victor-chew/rbx/freecad/servo/Printed_SG90_Servo_Connector/files/9g_conn_top.stl

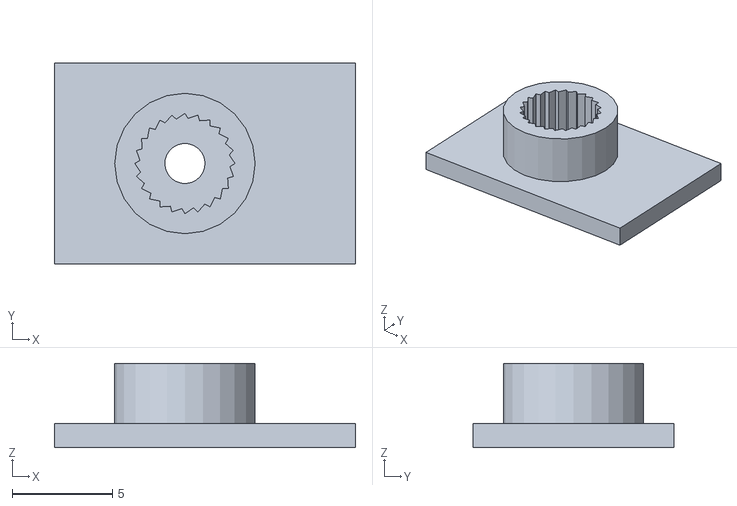
[picture p17: CAD file, 2021-03-17]
freecad/servo/Printed_SG90_Servo_Connector/files/9g_conn_top.stl
15.0 x 10.0 x 4.20
