victor-chew/rbx/freecad/sonar/back.stl

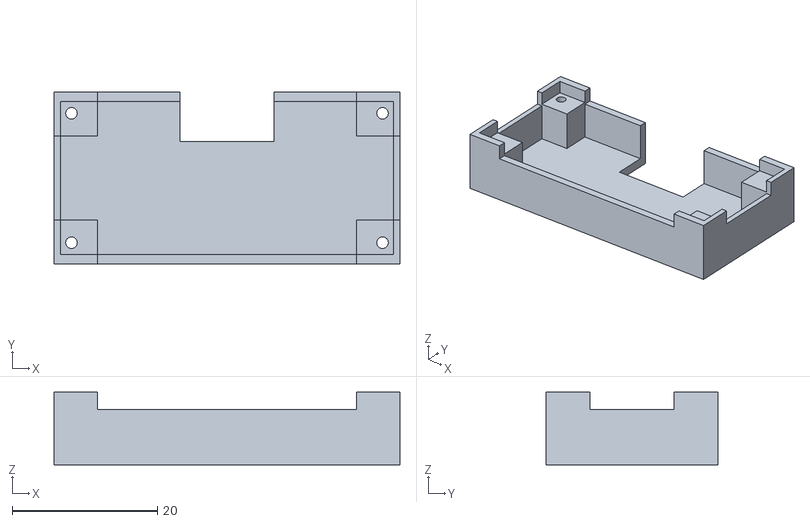
[picture p18: CAD file, 2021-03-17]
freecad/sonar/back.stl
47.6 x 23.6 x 10.0
