victor-chew/rbx/freecad/battery-18650/switch-cover.stl

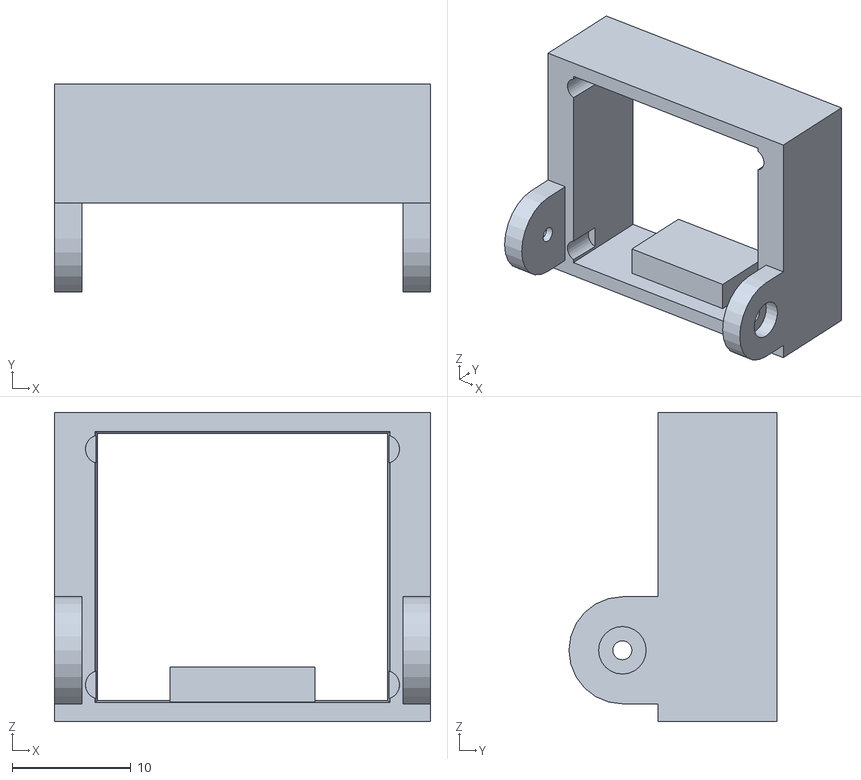
[picture p19: CAD file, 2021-03-17]
freecad/battery-18650/switch-cover.stl
31.6 x 17.5 x 26.0
