victor-chew/rbx/freecad/battery-AA/battery-AA.FCStd

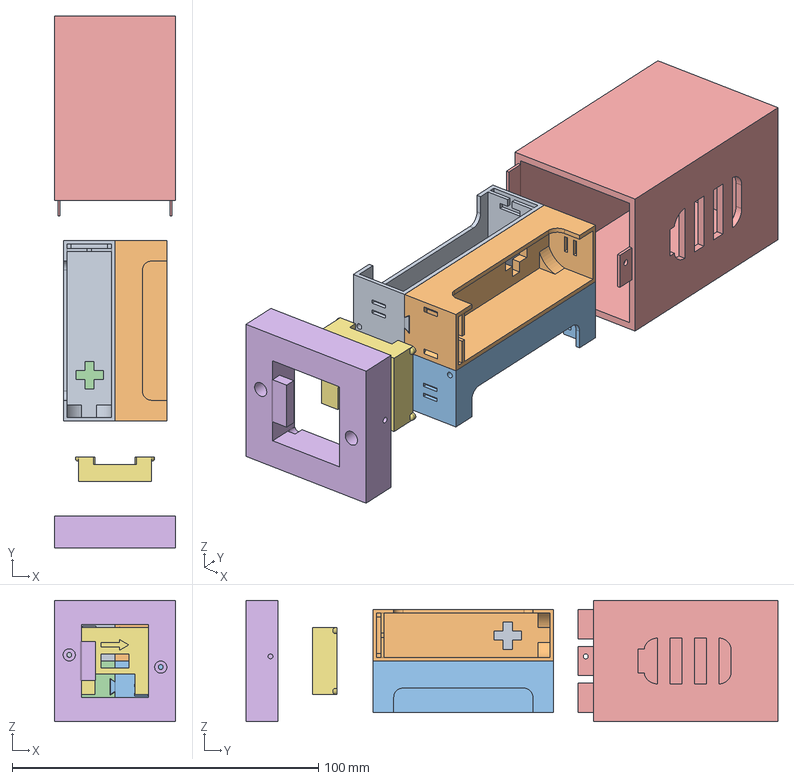
[picture p20: CAD file, 2021-03-17]
freecad/battery-AA/battery-AA.FCStd
39.6 x 173.8 x 39.6 mm
holder
holder-mirror
holder-clone
holder-clone-mirror
bottom
top
switch
