victor-chew/rbx/freecad/brickbase/3x1.3mf

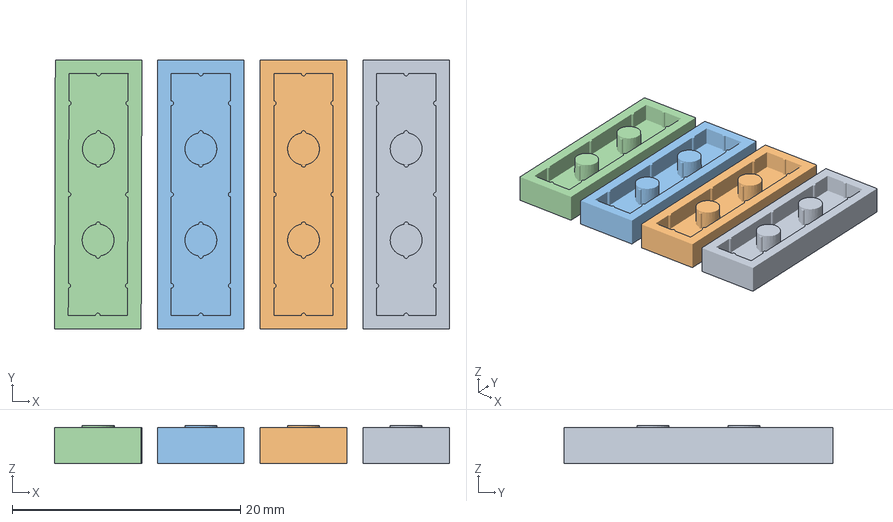
[picture p21: CAD file, 2021-03-17]
freecad/brickbase/3x1.3mf
34.6 x 23.6 x 3.36 mm
3x1.stl
3x1.stl(2)
3x1.stl(3)
3x1.stl(4)
