victor-chew/rbx/freecad/color-sensor/bottom.stl

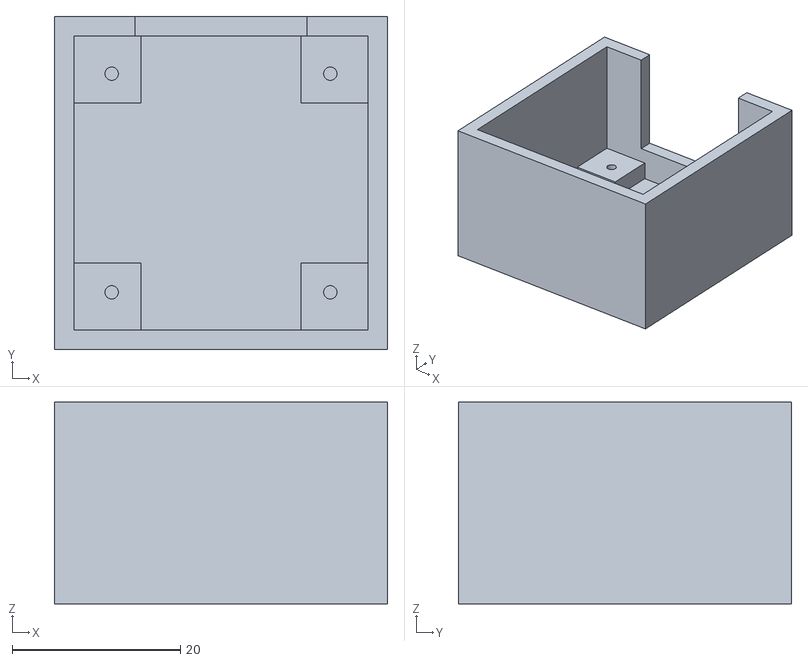
[picture p22: CAD file, 2021-03-17]
freecad/color-sensor/bottom.stl
39.6 x 39.6 x 24.0
