victor-chew/rbx/freecad/led/bottom.stl

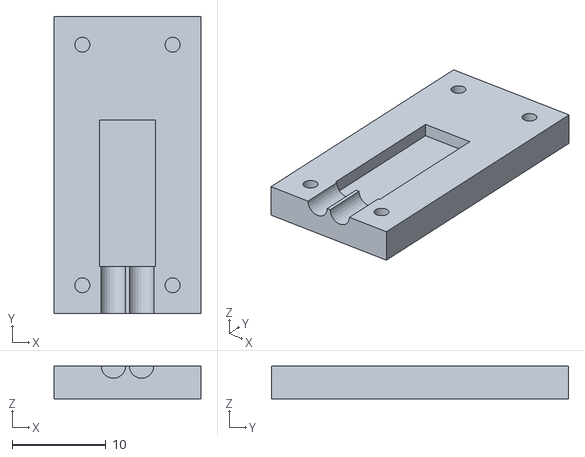
[picture p23: CAD file, 2021-03-17]
freecad/led/bottom.stl
15.6 x 31.6 x 3.50
