victor-chew/rbx/freecad/microcontroller/top.stl

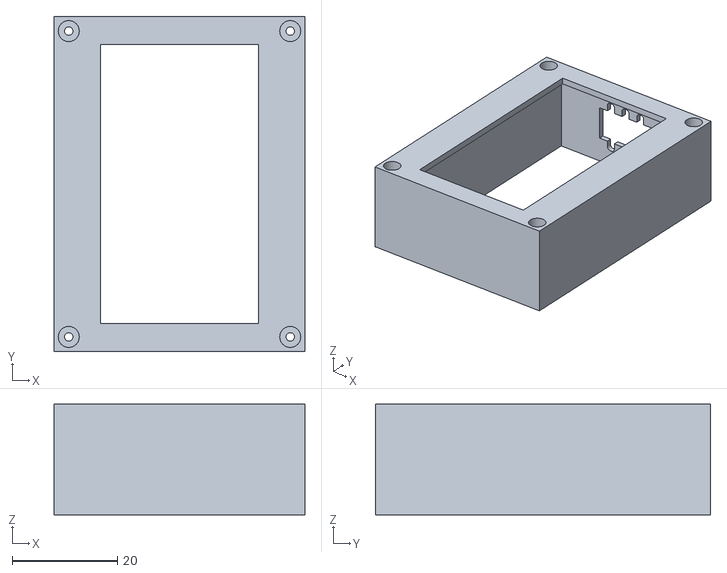
[picture p24: CAD file, 2021-03-17]
freecad/microcontroller/top.stl
47.6 x 63.6 x 21.0
