victor-chew/rbx/freecad/motor-power/motor-power.FCStd

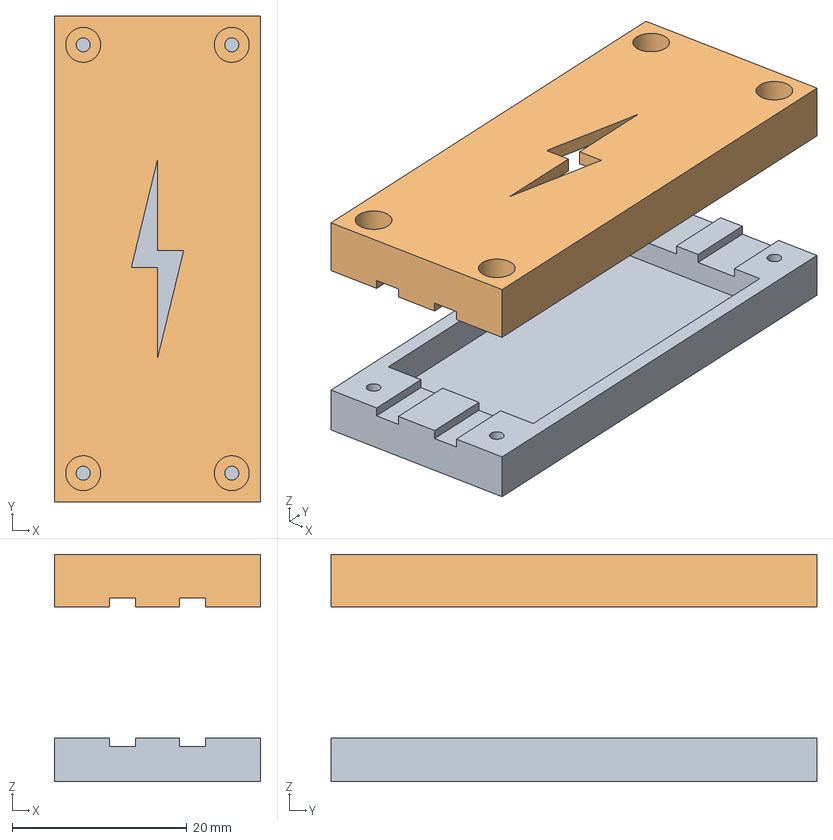
[picture p25: CAD file, 2021-03-17]
freecad/motor-power/motor-power.FCStd
23.6 x 55.6 x 26.0 mm
bottom
top
