victor-chew/rbx/freecad/motor/axle-adapter.stl

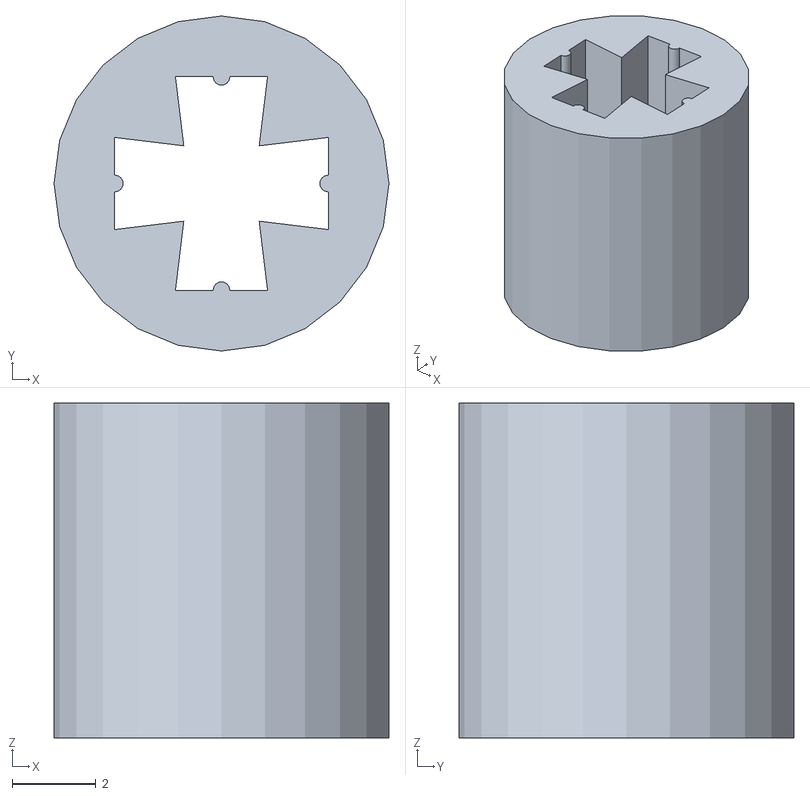
[picture p26: CAD file, 2021-03-17]
freecad/motor/axle-adapter.stl
8.00 x 8.00 x 8.00
