victor-chew/rbx/freecad/oled-display/top.stl

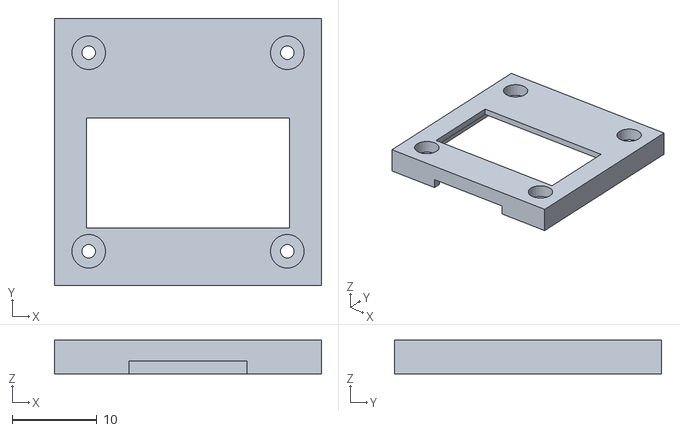
[picture p27: CAD file, 2021-03-17]
freecad/oled-display/top.stl
31.6 x 31.6 x 4.00
