victor-chew/rbx/freecad/photoresistor/top.stl

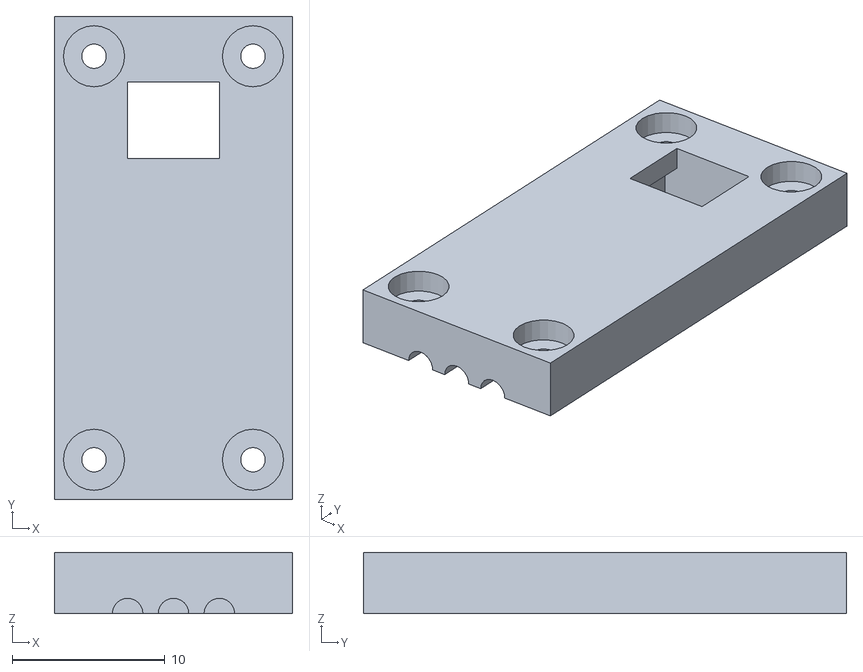
[picture p28: CAD file, 2021-03-17]
freecad/photoresistor/top.stl
15.6 x 31.6 x 4.00
