victor-chew/rbx/freecad/piezo-buzzer/bottom.stl

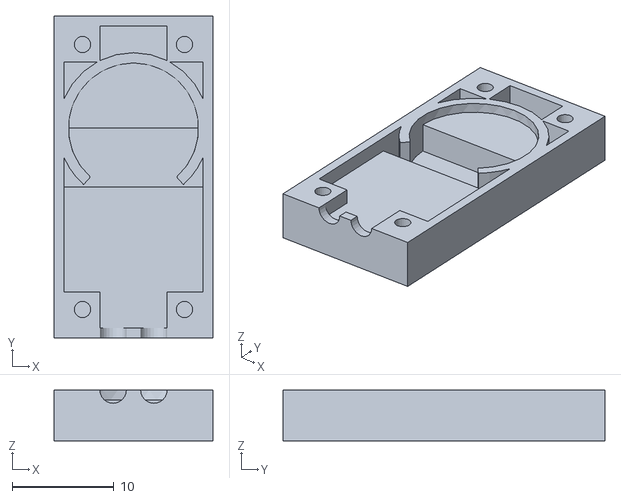
[picture p29: CAD file, 2021-03-17]
freecad/piezo-buzzer/bottom.stl
15.6 x 31.6 x 5.00
