victor-chew/rbx/freecad/pushbutton/top.stl

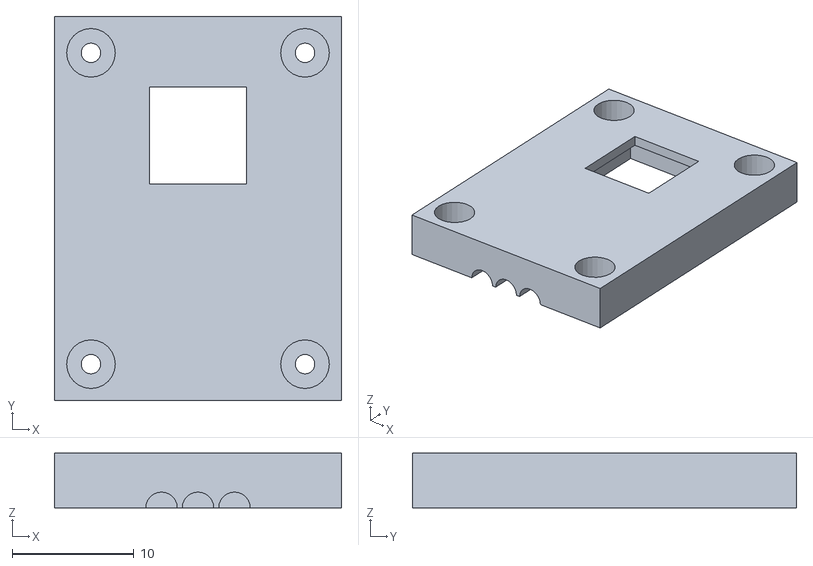
[picture p30: CAD file, 2021-03-17]
freecad/pushbutton/top.stl
23.6 x 31.6 x 4.50
