victor-chew/rbx/freecad/rotary-switch/bottom.stl

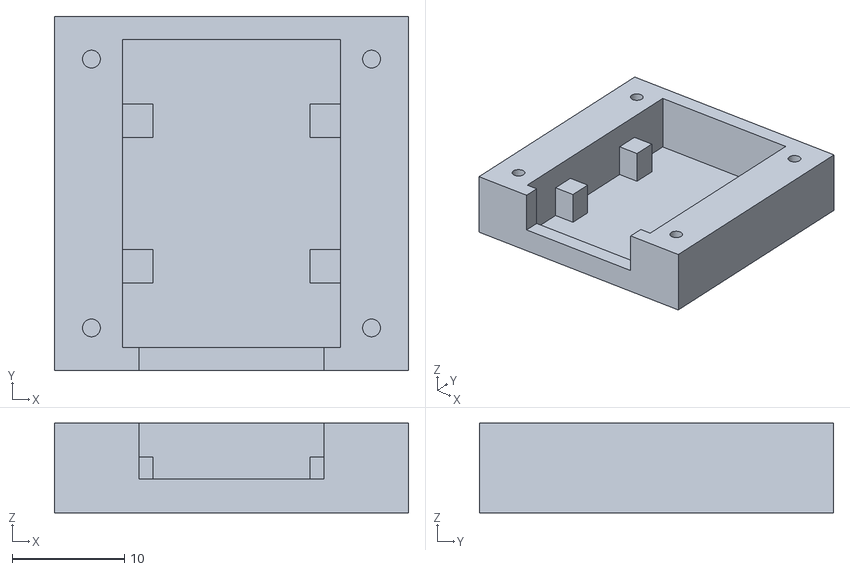
[picture p31: CAD file, 2021-03-17]
freecad/rotary-switch/bottom.stl
31.6 x 31.6 x 8.00
