victor-chew/rbx/freecad/servo/L-bracket.stl

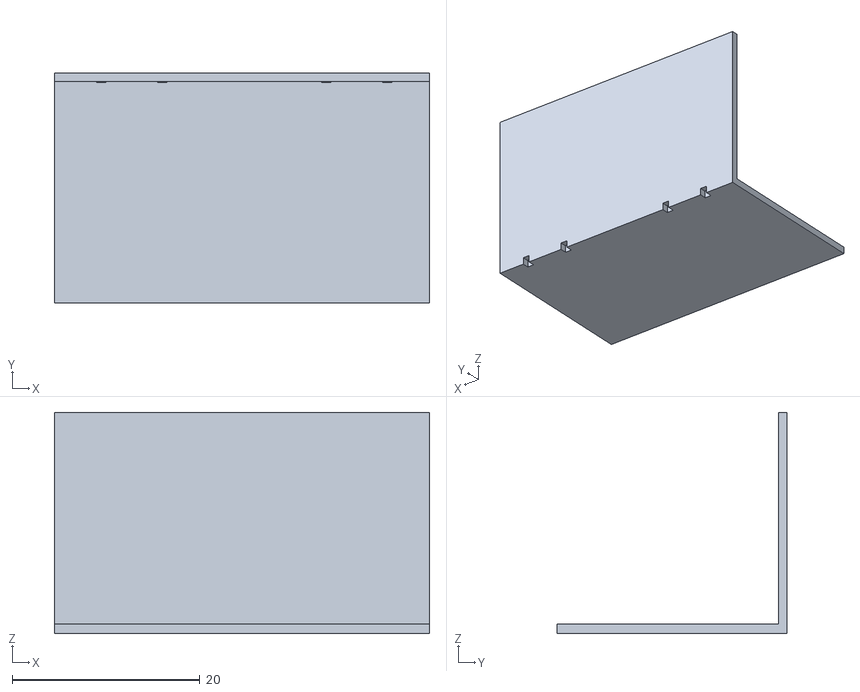
[picture p32: CAD file, 2021-03-17]
freecad/servo/L-bracket.stl
40.0 x 24.5 x 23.6
