victor-chew/rbx/freecad/sonar/front.stl

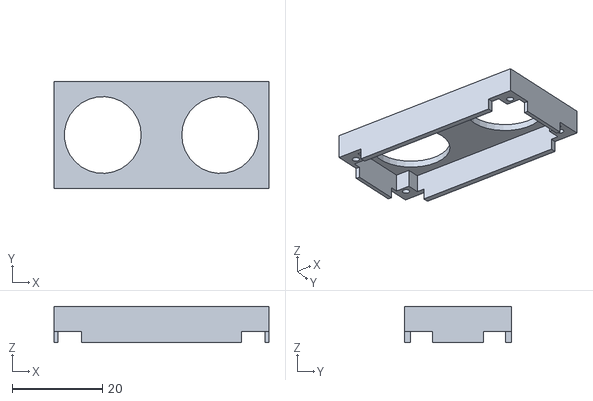
[picture p33: CAD file, 2021-03-17]
freecad/sonar/front.stl
47.6 x 23.6 x 8.00
