victor-chew/rbx/freecad/battery-18650/top.stl

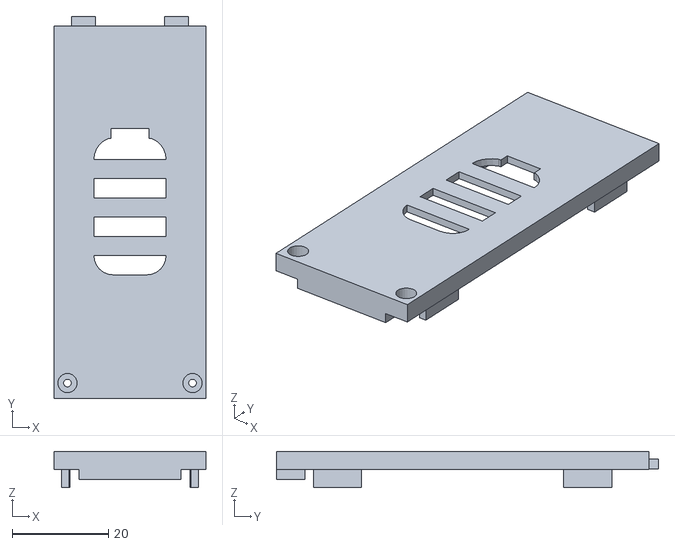
[picture p34: CAD file, 2021-03-17]
freecad/battery-18650/top.stl
31.6 x 79.5 x 7.50
