victor-chew/rbx/freecad/battery-AA/holder.stl

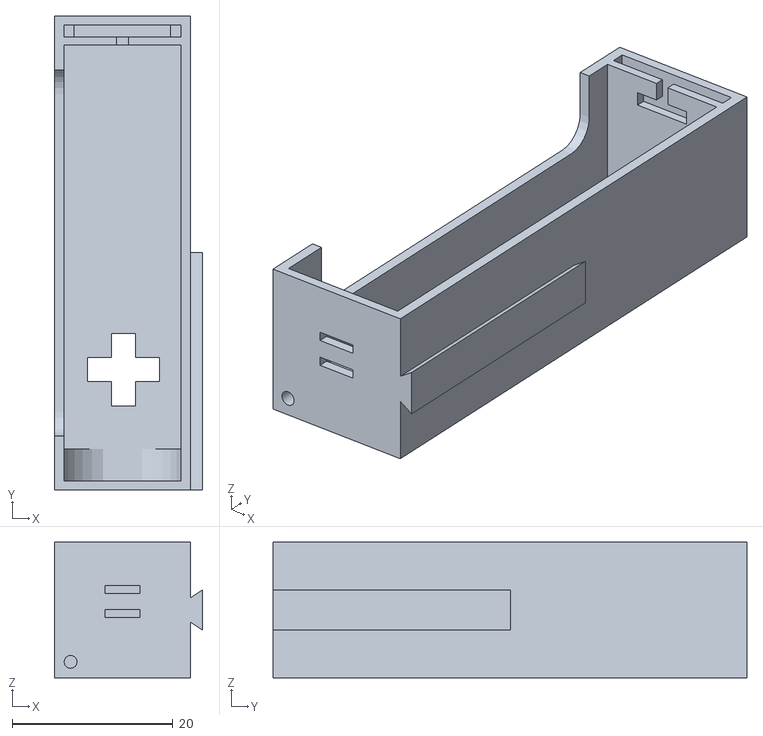
[picture p35: CAD file, 2021-03-17]
freecad/battery-AA/holder.stl
18.4 x 58.9 x 16.9
