victor-chew/rbx/freecad/brickbase/2x1.3mf

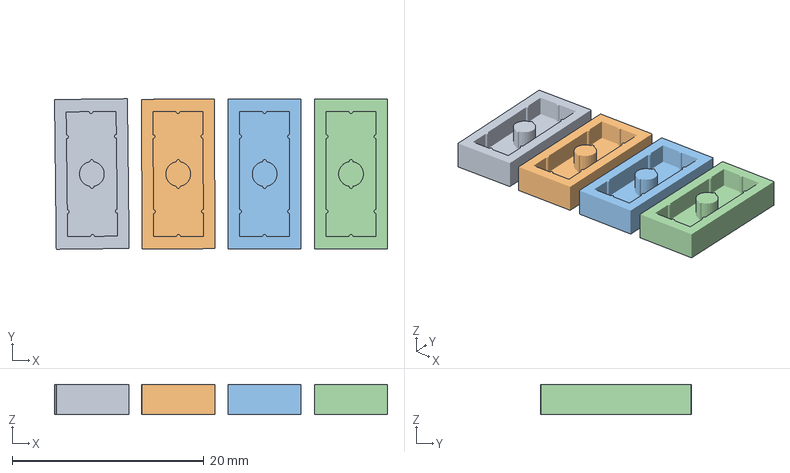
[picture p36: CAD file, 2021-03-17]
freecad/brickbase/2x1.3mf
34.7 x 15.7 x 3.16 mm
2x1.stl
2x1.stl(2)
2x1.stl(4)
2x1.stl(5)
