victor-chew/rbx/freecad/color-sensor/color-sensor.FCStd

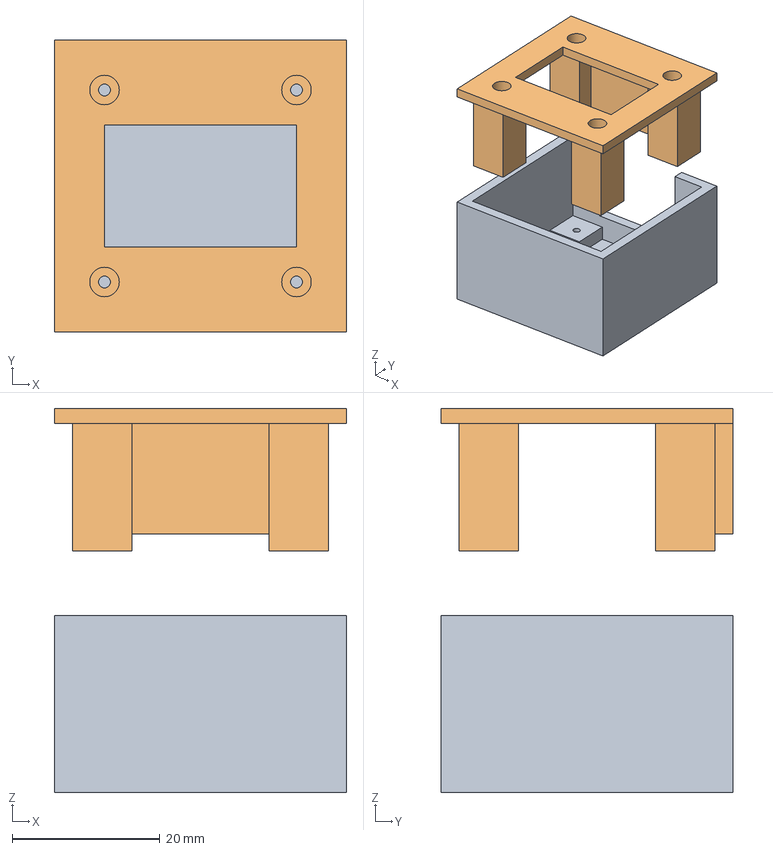
[picture p37: CAD file, 2021-03-17]
freecad/color-sensor/color-sensor.FCStd
39.6 x 39.6 x 52.0 mm
bottom
top
