victor-chew/rbx/freecad/led/top.stl

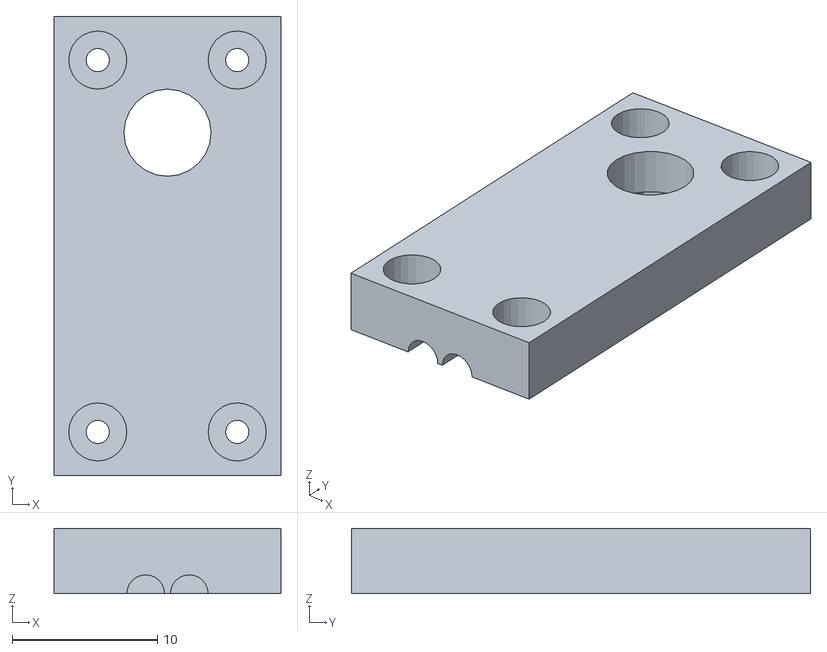
[picture p38: CAD file, 2021-03-17]
freecad/led/top.stl
15.6 x 31.6 x 4.50
