victor-chew/rbx/freecad/microcontroller/controller.FCStd

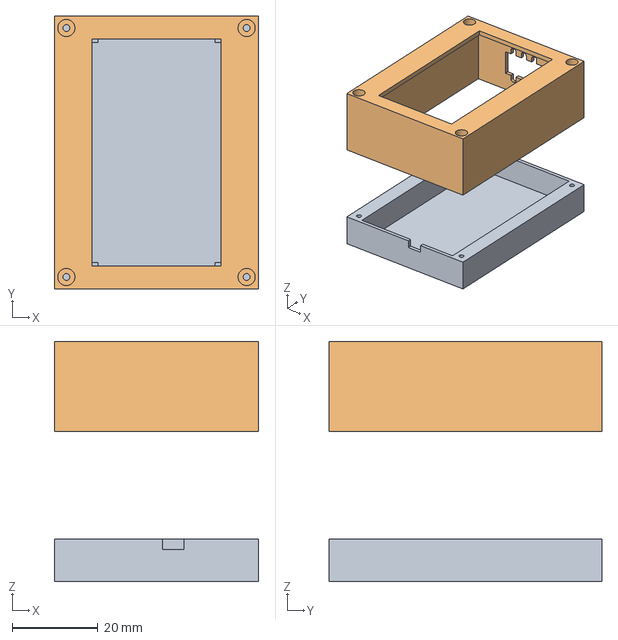
[picture p39: CAD file, 2021-03-17]
freecad/microcontroller/controller.FCStd
47.6 x 63.6 x 56.0 mm
bottom
top
