victor-chew/rbx/freecad/motor-power/top.stl

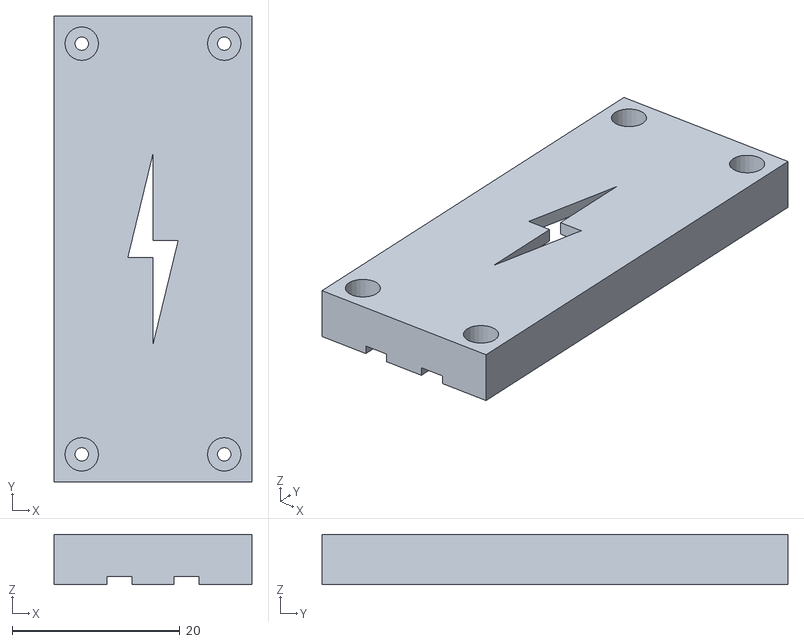
[picture p40: CAD file, 2021-03-17]
freecad/motor-power/top.stl
23.6 x 55.6 x 6.00
