victor-chew/rbx/freecad/motor/cover.stl

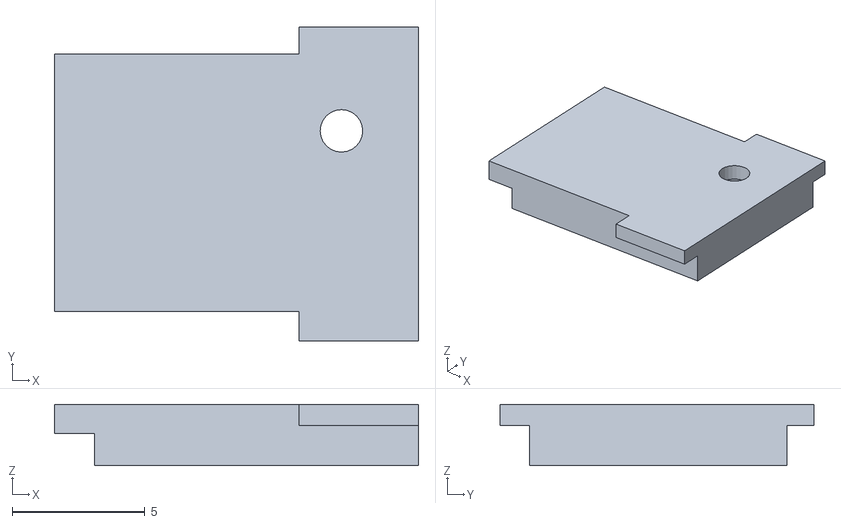
[picture p41: CAD file, 2021-03-17]
freecad/motor/cover.stl
13.7 x 11.8 x 2.30
