victor-chew/rbx/freecad/oled-display/bottom.stl

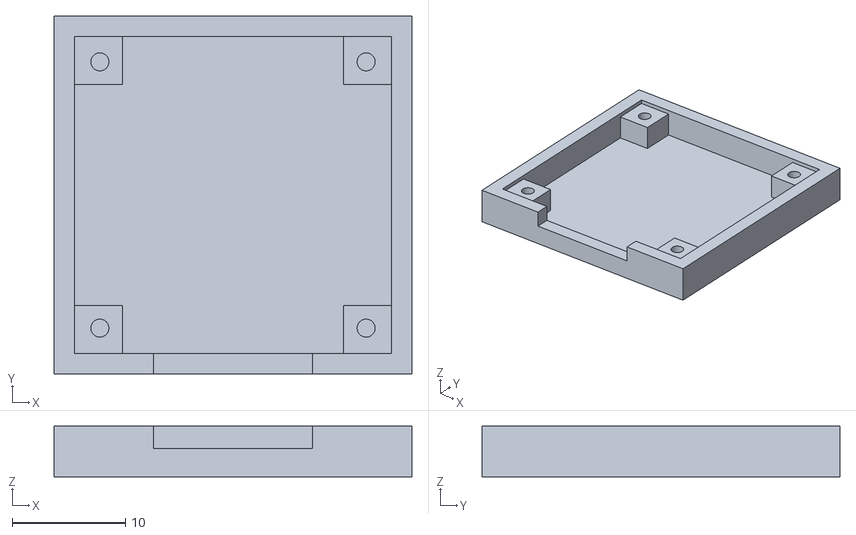
[picture p42: CAD file, 2021-03-17]
freecad/oled-display/bottom.stl
31.6 x 31.6 x 4.50
