victor-chew/rbx/freecad/photoresistor/photoresistor.FCStd

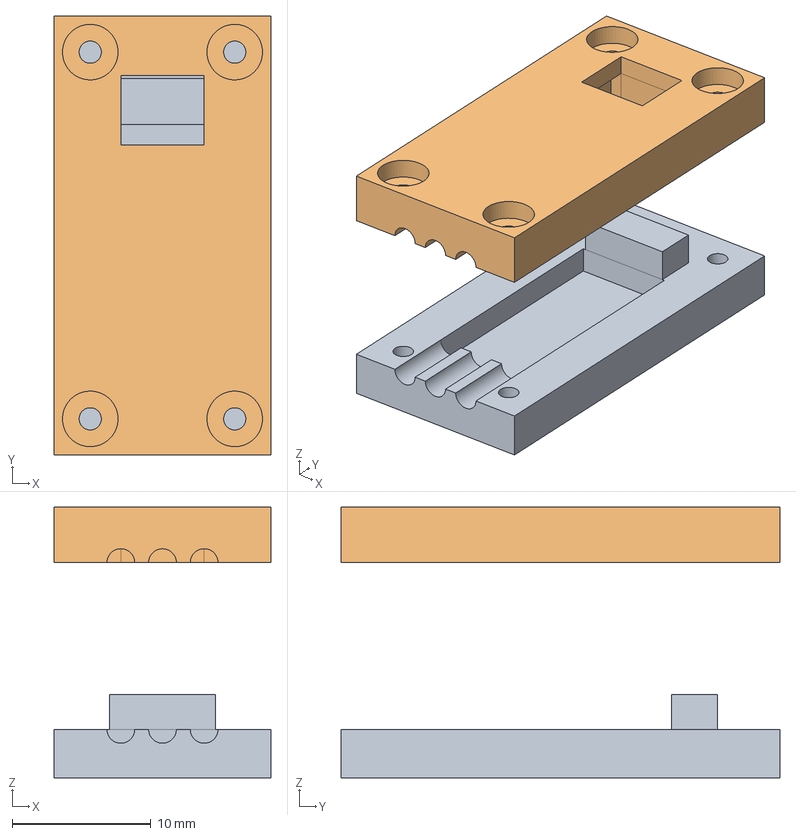
[picture p43: CAD file, 2021-03-17]
freecad/photoresistor/photoresistor.FCStd
15.6 x 31.6 x 19.5 mm
bottom
top
