victor-chew/rbx/freecad/piezo-buzzer/top.stl

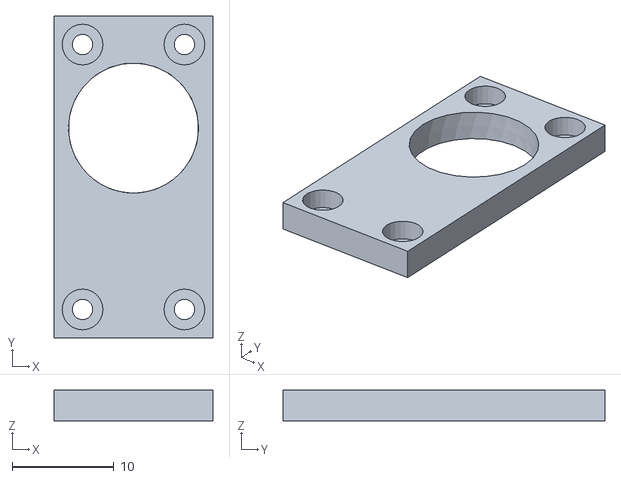
[picture p44: CAD file, 2021-03-17]
freecad/piezo-buzzer/top.stl
15.6 x 31.6 x 3.00
