victor-chew/rbx/freecad/pushbutton/bottom.stl

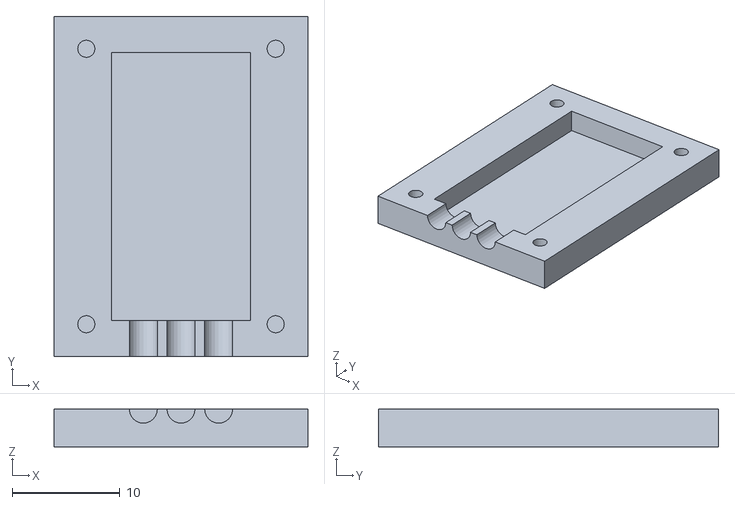
[picture p45: CAD file, 2021-03-17]
freecad/pushbutton/bottom.stl
23.6 x 31.6 x 3.50
