victor-chew/rbx/freecad/rotary-switch/top.stl

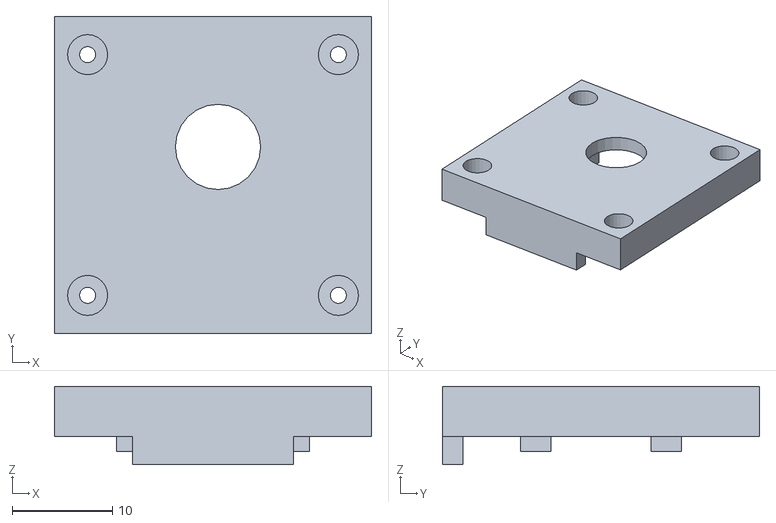
[picture p46: CAD file, 2021-03-17]
freecad/rotary-switch/top.stl
31.6 x 31.6 x 7.80
