victor-chew/rbx/freecad/servo/bottom.stl

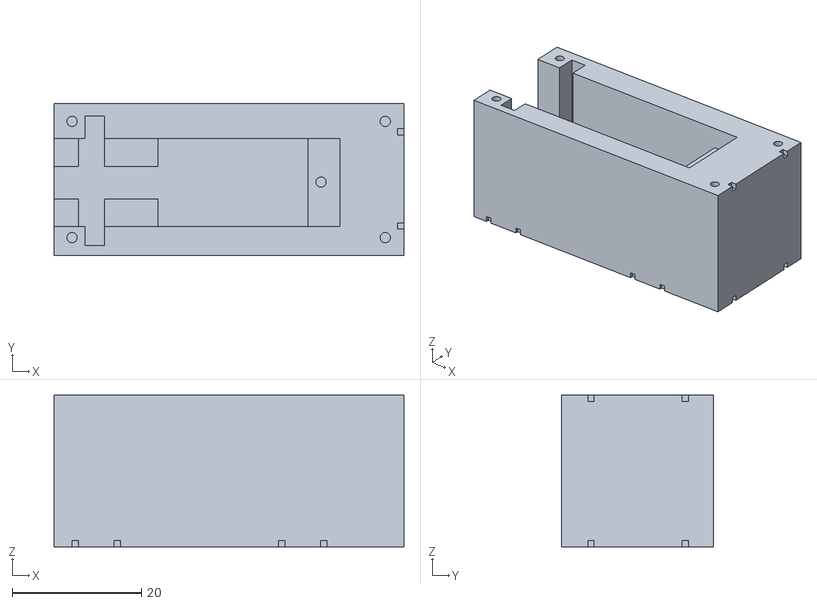
[picture p47: CAD file, 2021-03-17]
freecad/servo/bottom.stl
54.2 x 23.6 x 23.5
