victor-chew/rbx/freecad/sonar/wireholder.stl

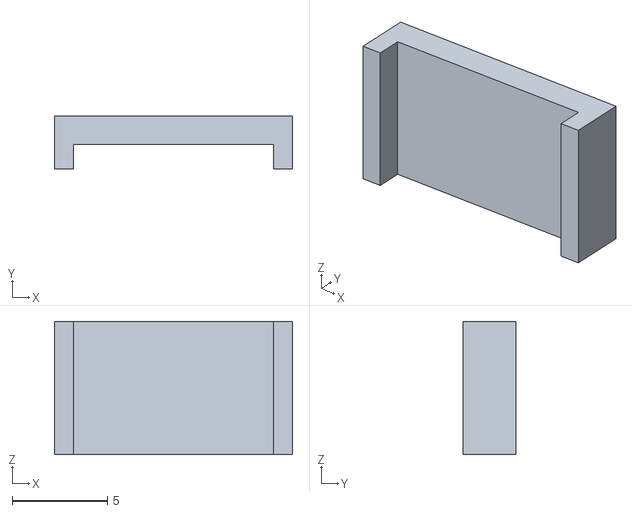
[picture p48: CAD file, 2021-03-17]
freecad/sonar/wireholder.stl
12.5 x 2.80 x 7.00
