victor-chew/rbx/freecad/battery-18650/bottom.stl

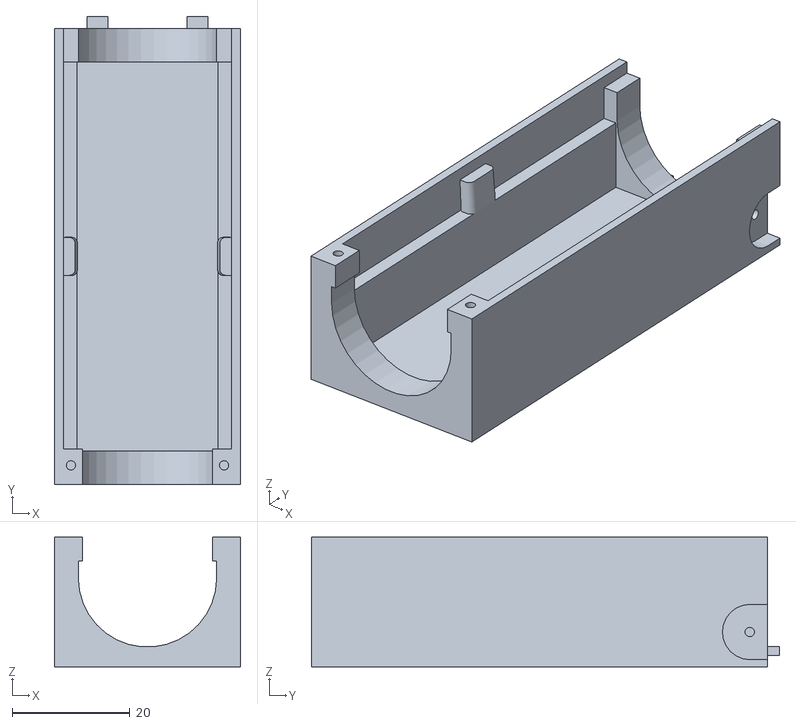
[picture p49: CAD file, 2021-03-17]
freecad/battery-18650/bottom.stl
31.6 x 79.5 x 22.0
