victor-chew/rbx/freecad/motor/axle-long.stl

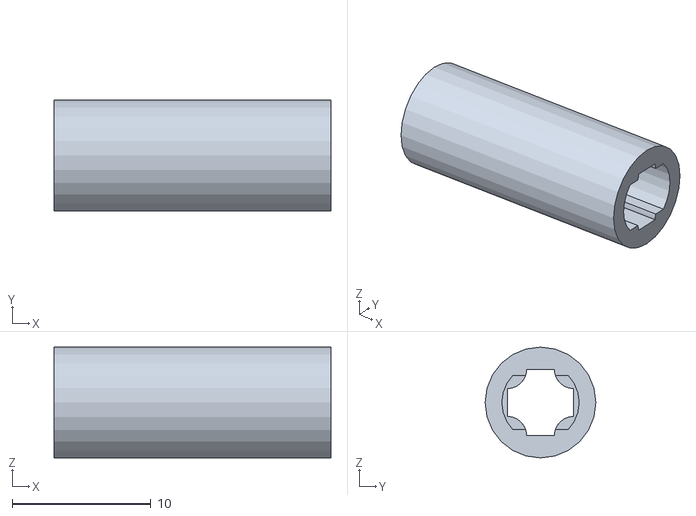
[picture p50: CAD file, 2021-03-17]
freecad/motor/axle-long.stl
20.0 x 8.00 x 8.00
