victor-chew/rbx/freecad/servo/front.stl

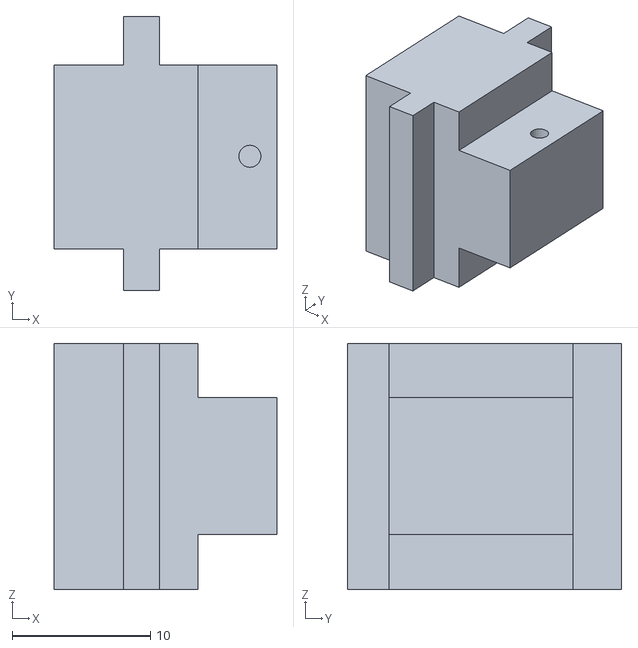
[picture p51: CAD file, 2021-03-17]
freecad/servo/front.stl
16.1 x 19.8 x 17.8
