victor-chew/rbx/freecad/sonar/sonar.FCStd

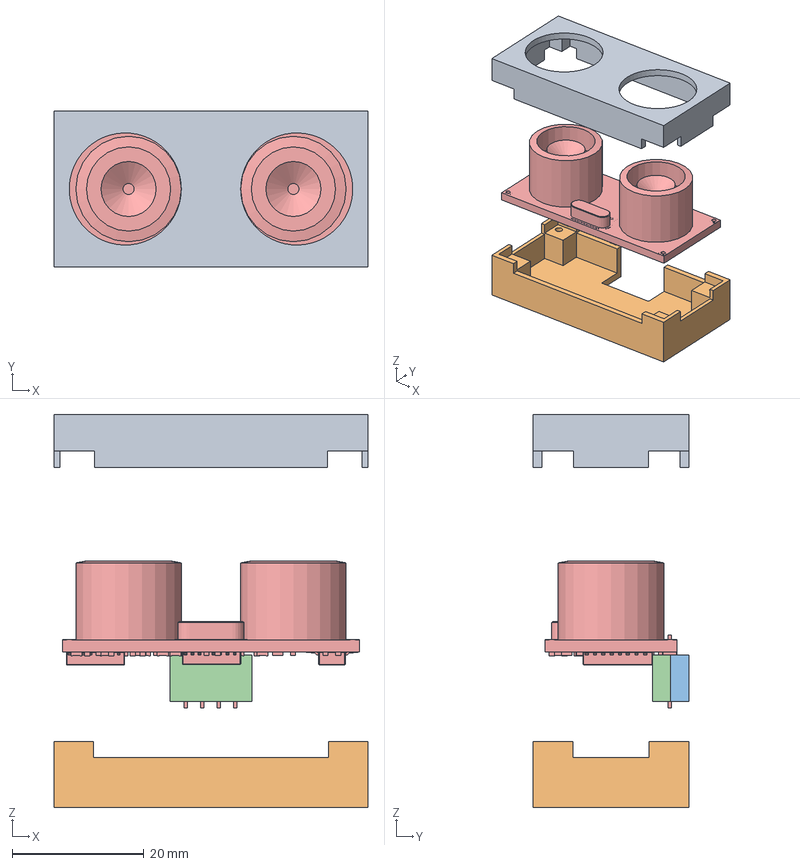
[picture p52: CAD file, 2021-03-17]
freecad/sonar/sonar.FCStd
47.6 x 23.6 x 59.6 mm
front
back
wh-bottom
wireholder-top
HC-SR04
