victor-chew/rbx/freecad/battery-18650/holder.stl

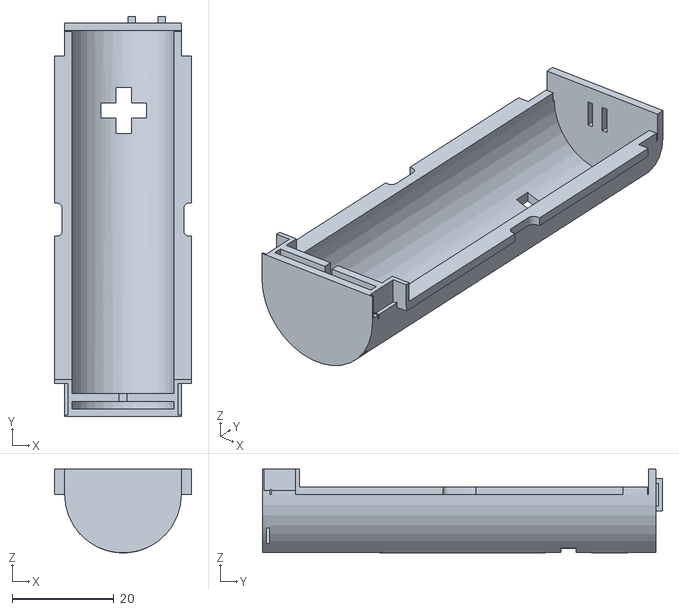
[picture p53: CAD file, 2021-03-17]
freecad/battery-18650/holder.stl
27.0 x 78.8 x 16.5
