victor-chew/rbx/freecad/motor/front.stl

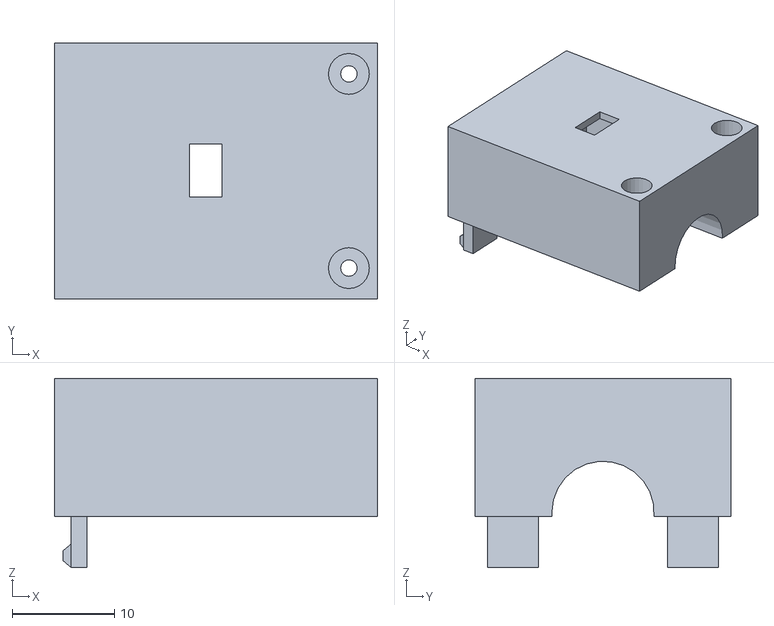
[picture p54: CAD file, 2021-03-17]
freecad/motor/front.stl
31.6 x 25.0 x 18.5
