victor-chew/rbx/freecad/servo/wire-holder-half.stl

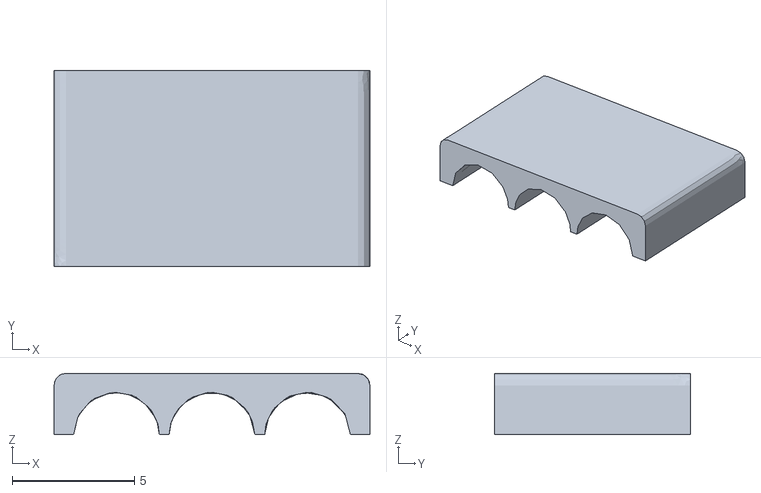
[picture p55: CAD file, 2021-03-17]
freecad/servo/wire-holder-half.stl
12.9 x 8.00 x 2.50
