victor-chew/rbx/freecad/battery-18650/battery-18650.FCStd

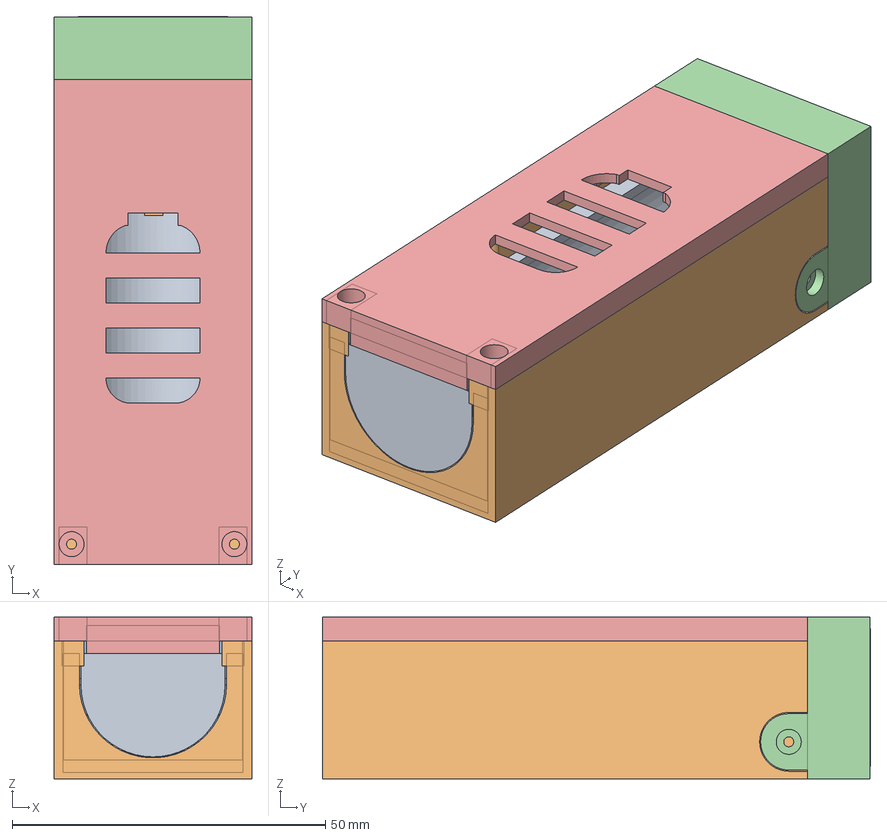
[picture p56: CAD file, 2021-03-17]
freecad/battery-18650/battery-18650.FCStd
31.6 x 87.5 x 25.8 mm
holder
bottom
switch
switch-cover
top
