victor-chew/rbx/freecad/motor/axle-short.stl

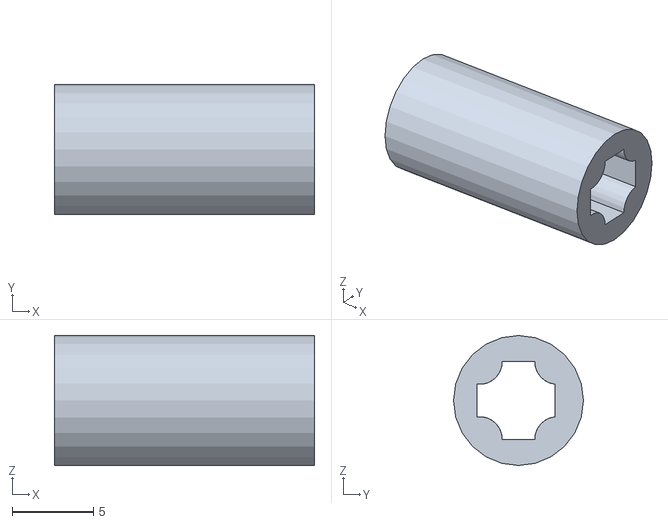
[picture p57: CAD file, 2021-03-17]
freecad/motor/axle-short.stl
16.0 x 8.00 x 8.00
