victor-chew/rbx/freecad/servo/sg90-connector.stl

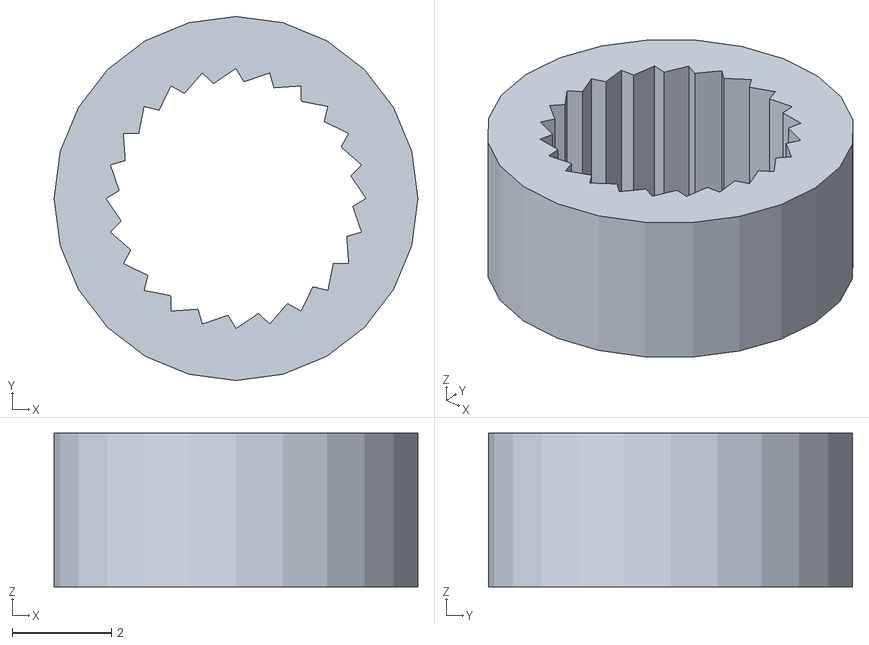
[picture p58: CAD file, 2021-03-17]
freecad/servo/sg90-connector.stl
7.35 x 7.35 x 3.11
