victor-chew/rbx/freecad/motor/back.stl

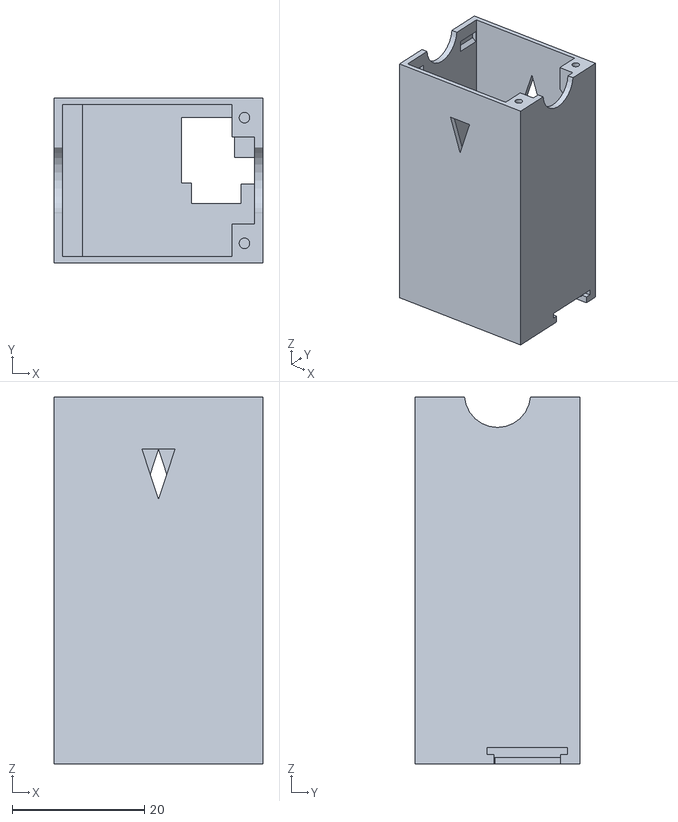
[picture p59: CAD file, 2021-03-17]
freecad/motor/back.stl
31.6 x 25.0 x 55.5
