victor-chew/rbx/freecad/servo/top.stl

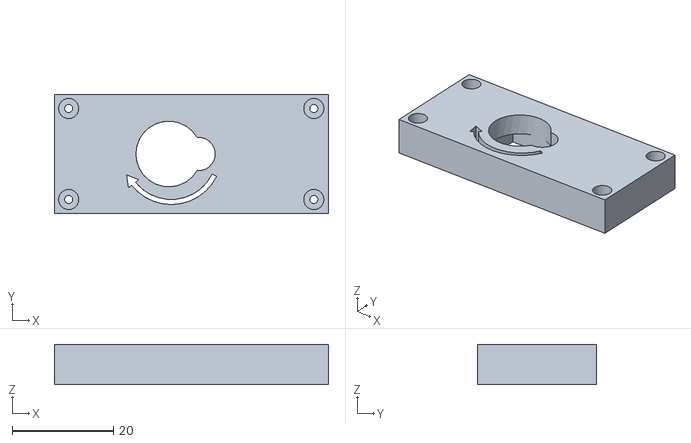
[picture p60: CAD file, 2021-03-17]
freecad/servo/top.stl
54.2 x 23.6 x 8.00
